banyaibalazs412/diplomamunka/greenHouseMonitoring/Core/Inc/mk_dht11.h

/**
 *  @file mk_dht11.h
 *	@brief DHT11 Library
 *  @date Created on: Oct 4, 2019
 *  @author Author: mesut.kilic
 *	@version 1.0.0
 */


#ifndef MK_DHT11_H_
#define MK_DHT11_H_

#include "stm32l452xx.h"
#include "main.h"

#define OUTPUT 1
#define INPUT 0

/**
 * @brief DHT11 struct
 */
struct _dht11_t{
	GPIO_TypeDef* port;	///GPIO Port ex:GPIOA
	uint16_t pin; ///GPIO pin ex:GPIO_PIN_2
	TIM_HandleTypeDef *htim; /// timer for measure time ex:htim3
	uint8_t temperature; ///Temperature value
	uint8_t humidty; ///humidity value
};
typedef struct _dht11_t dht11_t;


void init_dht11(dht11_t *dht, TIM_HandleTypeDef *htim, GPIO_TypeDef* port, uint16_t pin);
void set_dht11_gpio_mode(dht11_t *dht, uint8_t pMode);
uint8_t readDHT11(dht11_t *dht);

#endif /* MK_DHT11_H_ */
